GC-Lab-Gonzalo/Percu-Synth/Hardware/PCB_1-PCB_PCB_Percu-synth_V2.0.pdf

## PercuSynth V2.0 - PCB vista superior (TOP): ubicacion de componentes y serigrafia

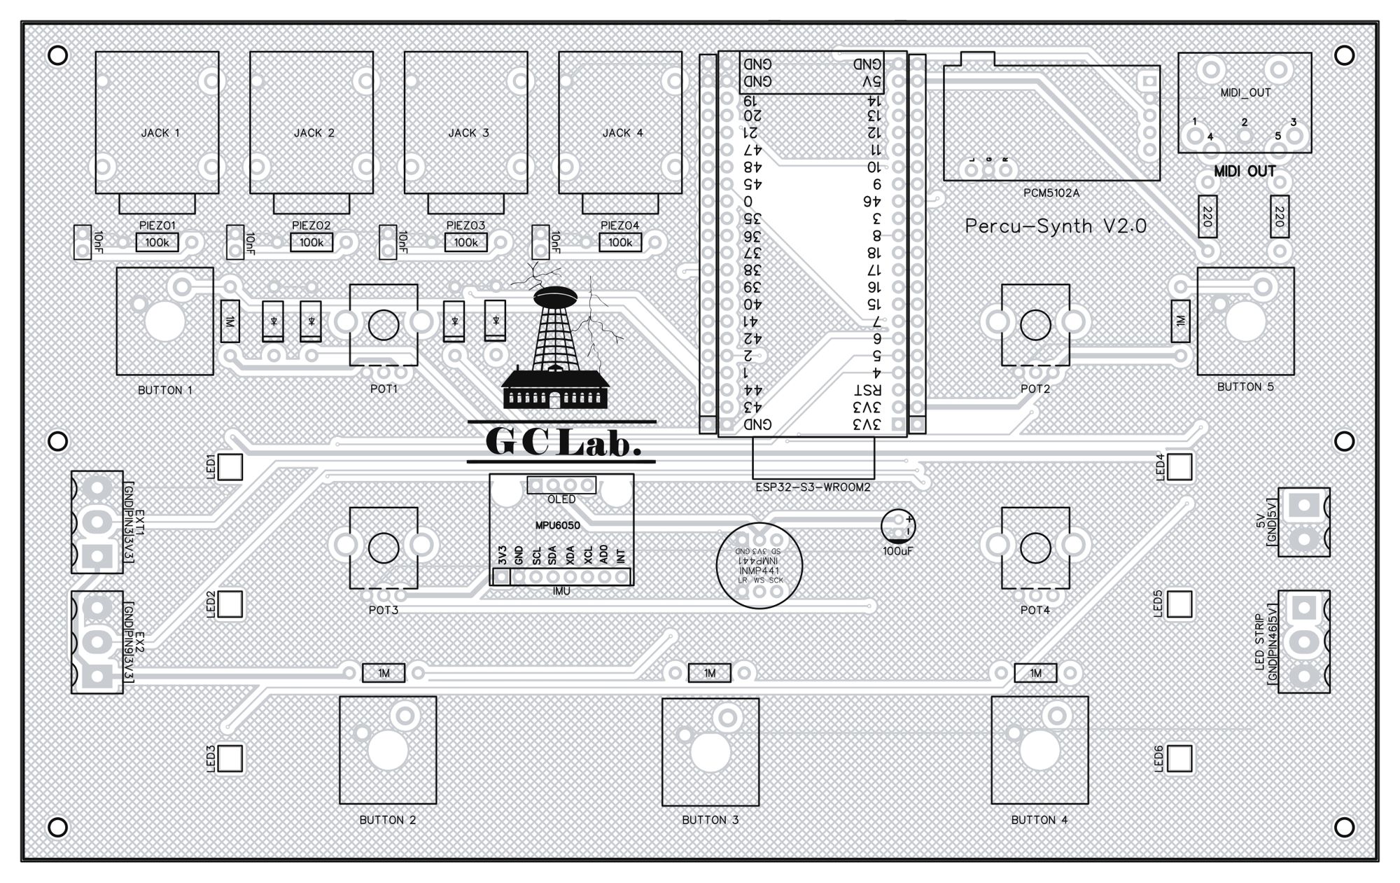
[picture p5: page 1]

GC Lab Chile - generado desde Gerber_Percu-synth_1-PCB_PCB_Percu-synth_V2.0.zip (2026-09-05). Placa de 200 x 125 mm.

## PercuSynth V2.0 - PCB vista inferior (BOTTOM), espejada tal como se ve por abajo

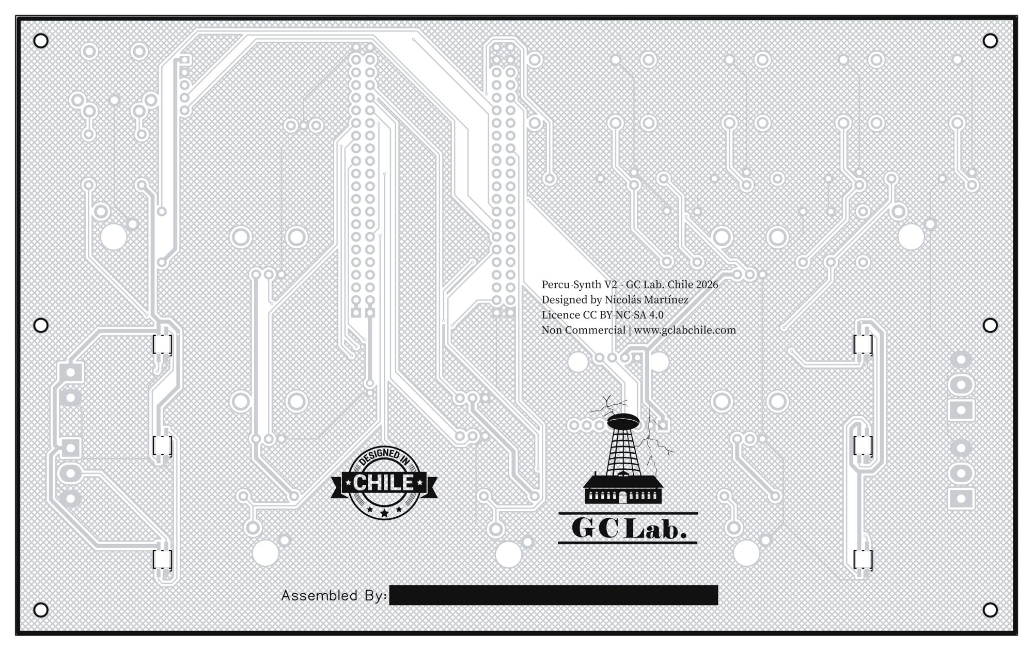
[picture p6: page 2]

GC Lab Chile - generado desde Gerber_Percu-synth_1-PCB_PCB_Percu-synth_V2.0.zip (2026-09-05). Placa de 200 x 125 mm.
