GC-Lab-Gonzalo/Percu-Synth/firmwares/pads_imu/Guia_Express_pads_imu.pdf

# Guía express · pads_imu

GC LAB CHILE — PercuSynth · Pads profundos polifónicos con arpegio · acordes sostenidos + filtro IMU (sin secuenciador)

Toca BTN1…BTN5 → cada botón enciende un acorde como pad

POT3 Release (cola larga) · POT4 Movimiento (respira).

Mueve el equipo en el aire → el IMU barre el filtro (filter sweep). Encadena botones para una progresión: DoM → SolM → Lam → FaM →

2 Los 3 paneles — combos para cambiar; el mismo combo te devuelve a A

PANEL | CÓMO ENTRAR | | PARA QUÉ
A tocar | al encender | A | tocar acordes · ataque · volumen · release · movimiento
B arpegio | BTN1 + BTN5 juntos | B | arpegio · transponer · octava · cambiar banco
C timbre | BTN2 + BTN4 juntos | C | forma de onda · capas · detune · tono · filtro

Al cambiar de panel los pots quedan congelados: cada uno retoma el control sólo cuando lo mueves (≈2 %). El acorde, el arpegio y el timbre persisten al volver al Panel A.

A Panel A | | | tocar

BTN1…
5

los 5 acordes del banco activo (latch: el mismo botón
| apaga)
POT1 | Ataque (5 ms → ~4 s de fundido)
POT2 | Volumen del pad (solo acordes)
POT3 | Release (~0.2 s → ~8 s de cola)
POT4 | Movimiento (LFO lento: respira filtro + tremolo)
B Panel B | arpegio
POT1 | Volumen del arpegio (en 0 = apagado) — independiente
del pad
POT2 | Velocidad (2 → 16 notas/s)
POT3 | Rango de octavas (1 → 3)
POT4 | Gate (largo de cada nota)

Botones BTN1/BTN5 transponer ∓1 · BTN2/BTN4 octava ∓1 · BTN3 cambiar banco

El arpegio recorre las notas del acorde que esté sonando.

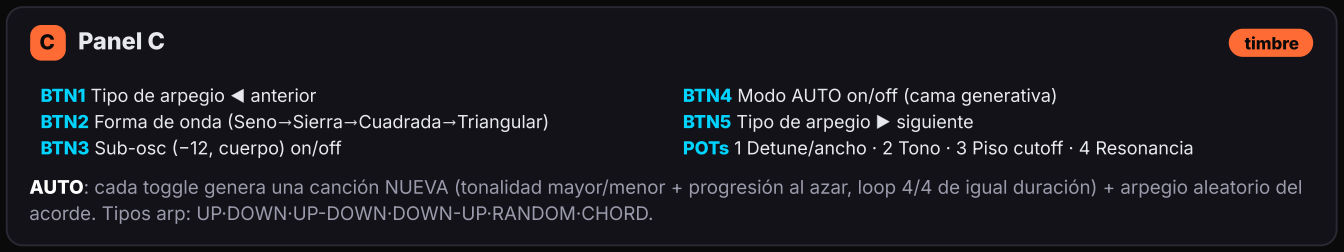
[picture p7: figure]
C Panel C; timbre; BTN1 Tipo de arpegio ◀ anterior BTN2 Forma de onda (Seno→Sierra→Cuadrada→Triangular) BTN3 Sub-osc (−12, cuerpo) on/off; BTN4 Modo AUTO on/off (cama generativa) BTN5 Tipo de arpegio ▶ siguiente; acorde. Tipos arp: UP·DOWN·UP-DOWN·DOWN-UP·RANDOM·CHORD.

POTs 1 Detune/ancho · 2 Tono · 3 Piso cutoff · 4 Resonancia

AUTO: cada toggle genera una canción NUEVA (tonalidad mayor/menor + progresión al azar, loop 4/4 de igual duración) + arpegio aleatorio del

3 Bancos (BTN3 Panel B cicla los 5, sin reiniciar)

| B0 | B1 | B2 | B3 | B4
BTN1 | Do M | Do M | Do M | Re m | Mi M
BTN2 | Sol M | La m | Mi M | Si♭ M | Mi m
BTN3 | La m | Mi7 | Fa M | La M | Si M
BTN4 | Fa M | Fa M | Fa m | Do M | Si m
BTN5 | Re m | Sol M | Mi m | Fa M | Do M
BTN1+3 | Mi m | Re m | Sol M | Sol m | Re M

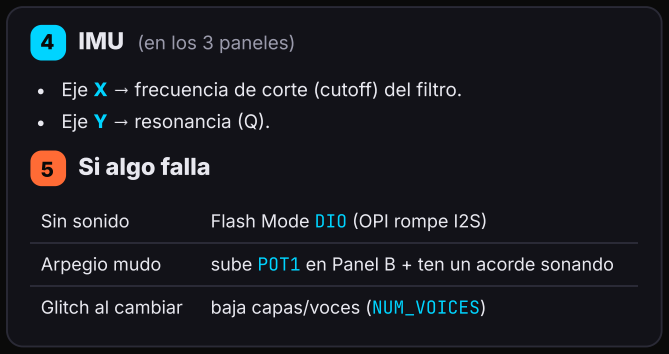
[picture p8: figure]
4 IMU (en los 3 paneles); Eje Y → resonancia (Q).; 5 Si algo falla; Glitch al cambiar; baja capas/voces (NUM_VOICES)

Eje X → frecuencia de corte (cutoff) del filtro.

Sin sonido | Flash Mode DIO (OPI rompe I2S)
Arpegio mudo | sube POT1 en Panel B + ten un acorde sonando
PercuSynth · GC Lab Chile · firmware pads_imu | ESP32-S3 · I2S→PCM5102 44.1 kHz · 32 voces estéreo · sin LEDs
