GC-Lab-Gonzalo/Percu-Synth/firmwares/trance_imu_leds/Guia_Express_trance_imu_leds.pdf

# Guía express · trance_imu_leds

GC LAB CHILE — PercuSynth · Secuenciador de trance polifónico con visualizador en los 6 LEDs de la placa

BTN1 → Play. Suena la secuencia y los LEDs se mueven.

POT4 → cola/decay (súbelo para textura densa).

Mueve el equipo en el aire → el IMU barre el filtro y cambia el color. BTN2 escala · BTN3 patrón · BTN5 octava.

2 Los 3 paneles — el color del LED te dice dónde estás

PANEL | CÓMO ENTRAR | COLOR LEDS | PARA QUÉ
A normal | al encender | CIAN | tocar · tempo · escala · patrón · octava
B notas | BTN1 + BTN5 juntos | VIOLETA | cambiar tonalidad y armar el acorde
C timbre | BTN2 + BTN4 juntos | NARANJA | forma de onda · capas · detune · drive

El mismo combo te devuelve al Panel A (un flash lo confirma). Al cambiar de panel los pots quedan congelados: cada uno retoma el control sólo cuando lo mueves.

3 Panel A | | tocar
BTN1 | Play / Stop
BTN2 | Escala (Mayor·Menor·Armónica·Árabe·Lidia·Frigia)
BTN3 | Patrón (16)
BTN4 | Largo de secuencia (4→8→16)
BTN5 | Octava (-1→0→+1→+2)
POTs | 1 Ataque · 2 Volumen · 3 Tempo · 4 Decay

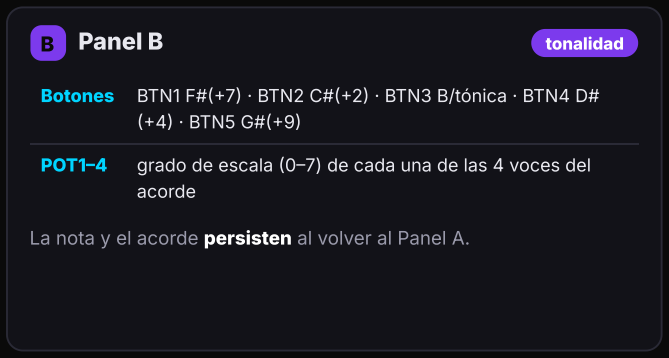
[picture p9: figure]
B Panel B; tonalidad; (+4) · BTN5 G#(+9); acorde

Botones BTN1 F#(+7) · BTN2 C#(+2) · BTN3 B/tónica · BTN4 D#

POT1–4 grado de escala (0–7) de cada una de las 4 voces del

La nota y el acorde persisten al volver al Panel A.

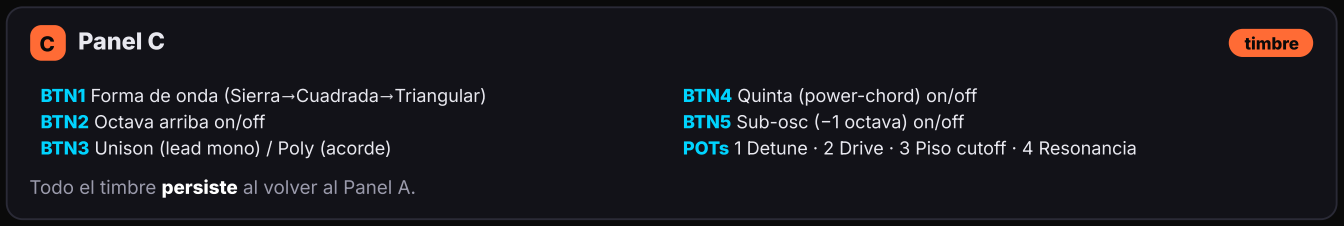
[picture p10: figure]
C Panel C; timbre; BTN1 Forma de onda (Sierra→Cuadrada→Triangular) BTN2 Octava arriba on/off BTN3 Unison (lead mono) / Poly (acorde); BTN4 Quinta (power-chord) on/off BTN5 Sub-osc (−1 octava) on/off

POTs 1 Detune · 2 Drive · 3 Piso cutoff · 4 Resonancia

Todo el timbre persiste al volver al Panel A.

4 Qué muestran los 6 LEDs | ● ● ● ● | ● ●

Color = panel (cian/violeta/naranja) + el filtro del IMU lo desplaza al moverte.
Barra (cuántos encienden) = energía polifónica: más acorde/cola → más llena.
Destello = cada beat; el downbeat (1·5·9·13) pega más fuerte. Detenido = respiración lenta en el color del panel.

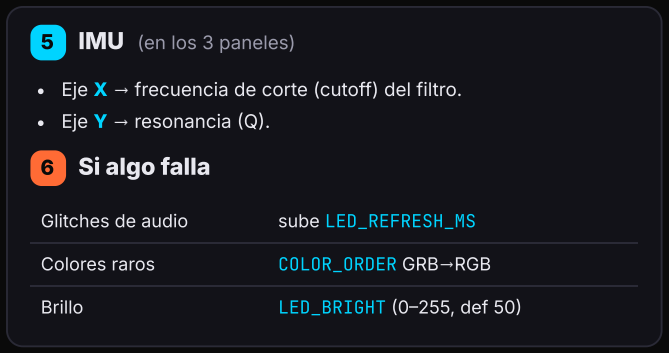
[picture p11: figure]
5 IMU (en los 3 paneles); Eje Y → resonancia (Q).; 6 Si algo falla; Glitches de audio; sube LED_REFRESH_MS; Colores raros; COLOR_ORDER GRB→RGB; Brillo; LED_BRIGHT (0–255, def 50)

Eje X → frecuencia de corte (cutoff) del filtro.

PercuSynth · GC Lab Chile · firmware trance_imu_leds | ESP32-S3 · I2S→PCM5102 44.1 kHz · 16 voces · WS2812 ×6
